galah-x/dashdisplay/pics/07_rear_and_front_asy_initial.jpg

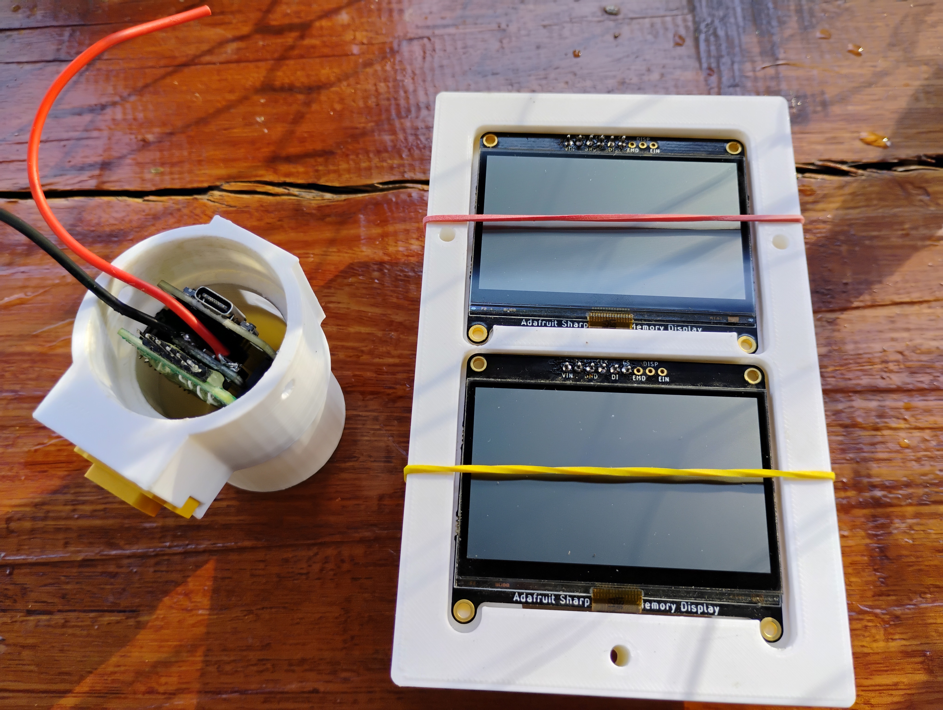
pics/07_rear_and_front_asy_initial.jpg
