galah-x/dashdisplay/pics/12_working_with_watchmon.jpg

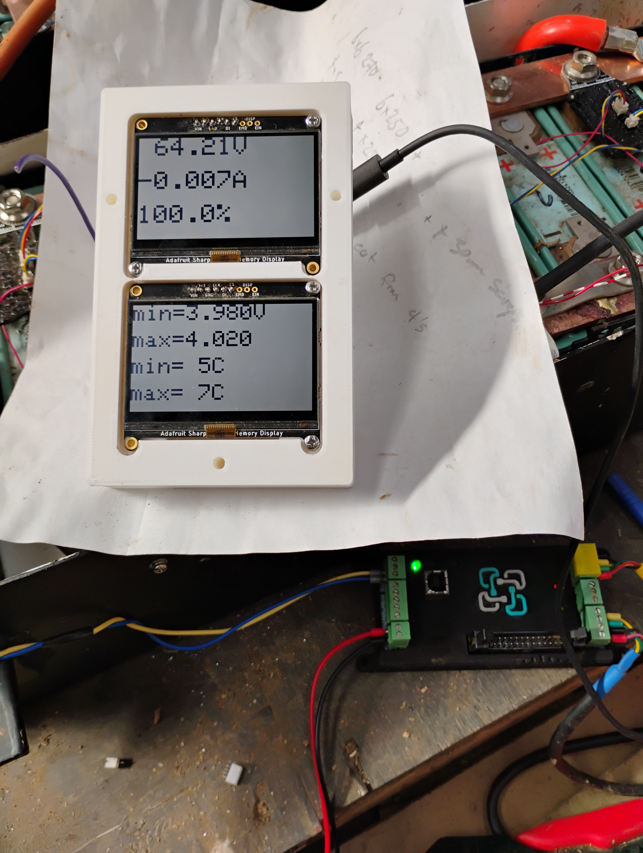
pics/12_working_with_watchmon.jpg
