galah-x/dashdisplay/pics/06_display_wiring_bd_fitted.jpg

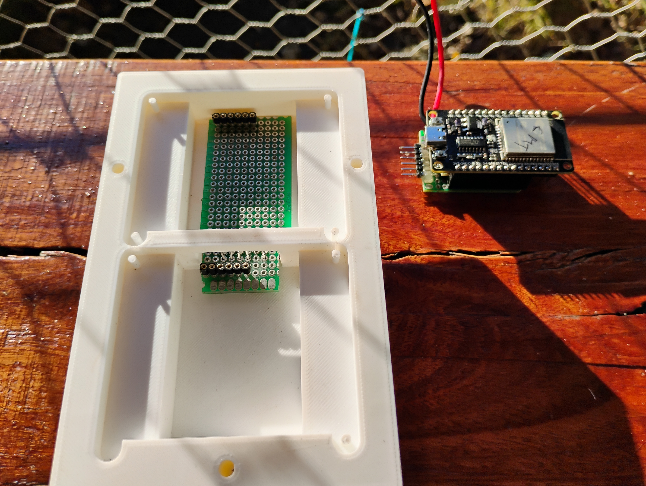
pics/06_display_wiring_bd_fitted.jpg
