galah-x/dashdisplay/schematics/dashdisplay_lcd_wiring/dashdisplay_lcd_wiring.kicad_sch

## KiCad design schematics/dashdisplay_lcd_wiring/dashdisplay_lcd_wiring.kicad_sch (2025-06-19)

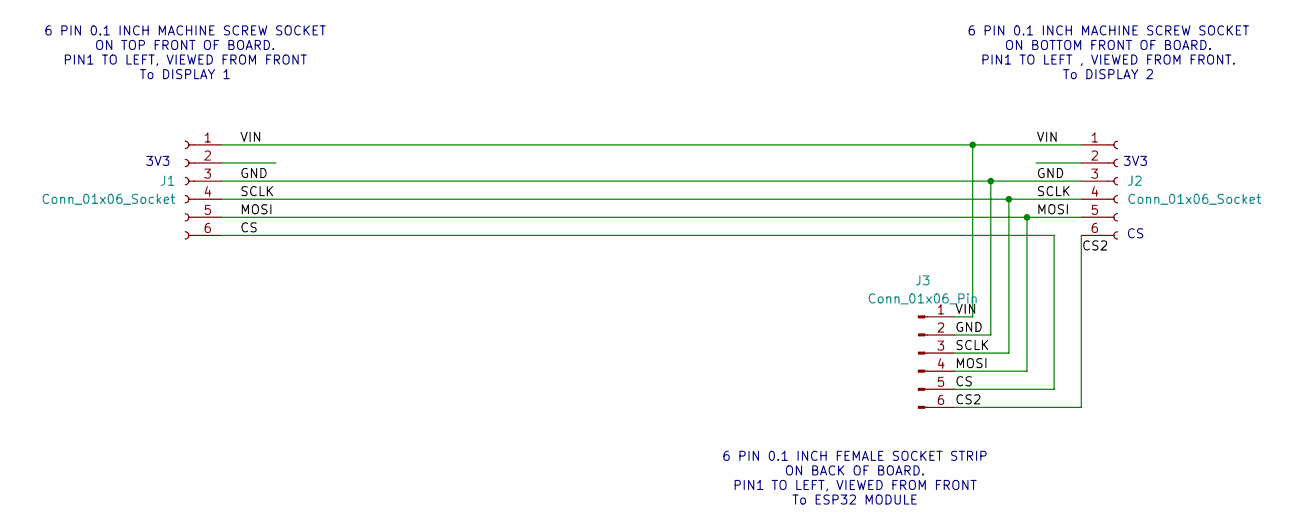
[picture p16: schematic dashdisplay_lcd_wiring.kicad_sch]

Parts:
J1, J2: Conn_01x06_Socket
J3: Conn_01x06_Pin

Connections:
CS: J1.6, J3.5
CS2: J2.6, J3.6
GND: J1.3, J2.3, J3.2
MOSI: J1.5, J2.5, J3.4
SCLK: J1.4, J2.4, J3.3
VIN: J1.1, J2.1, J3.1

Notes on the sheet:
6 PIN 0.1 INCH MACHINE SCREW SOCKET ON BOTTOM FRONT OF BOARD. PIN1 TO LEFT , VIEWED FROM FRONT. To DISPLAY 2
6 PIN 0.1 INCH FEMALE SOCKET STRIP ON BACK OF BOARD. PIN1 TO LEFT, VIEWED FROM FRONT To ESP32 MODULE
3V3
6 PIN 0.1 INCH MACHINE SCREW SOCKET ON TOP FRONT OF BOARD. PIN1 TO LEFT, VIEWED FROM FRONT To DISPLAY 1
