galah-x/dashdisplay/schematics/dashdisplay_motherboard/dashdisplay_motherboard.kicad_sch

## KiCad design schematics/dashdisplay_motherboard/dashdisplay_motherboard.kicad_sch (2025-06-19)

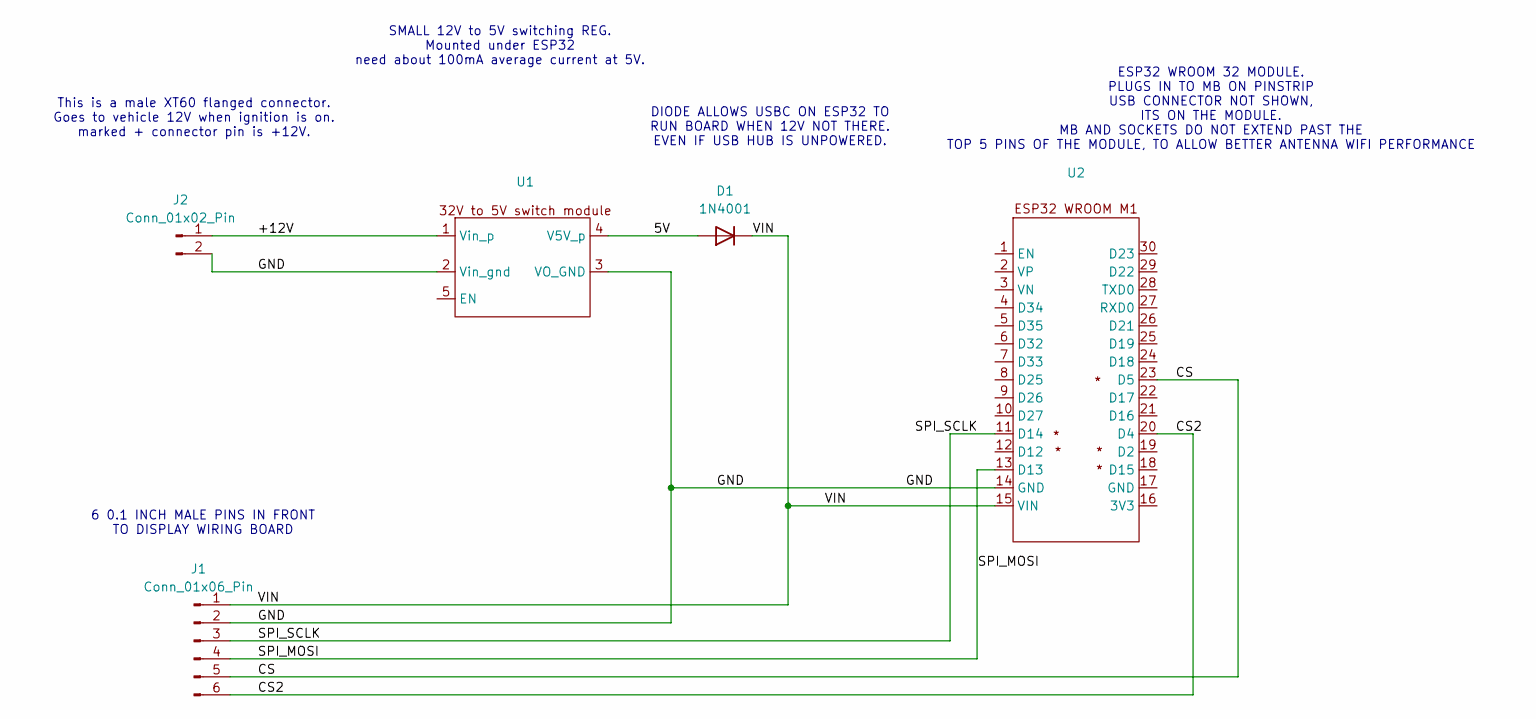
[picture p17: schematic dashdisplay_motherboard.kicad_sch]

Parts:
D1: 1N4001; D_DO-41_SOD81_P10.16mm_Horizontal
J1: Conn_01x06_Pin
J2: Conn_01x02_Pin
U1: switcher_en
U2: (no value)

Connections:
5V: D1.2 (A), U1.4 (V5V_p)
+12V: J2.1, U1.1 (Vin_p)
CS: J1.5, U2.23 (D5)
CS2: J1.6, U2.20 (D4)
GND: J1.2, J2.2, U1.2 (Vin_gnd), U1.3 (VO_GND), U2.14 (GND)
SPI_MOSI: J1.4, U2.13 (D13)
SPI_SCLK: J1.3, U2.11 (D14)
VIN: D1.1 (K), J1.1, U2.15 (VIN)

Notes on the sheet:
SMALL 12V to 5V switching REG. Mounted under ESP32 need about 100mA average current at 5V.
ESP32 WROOM 32 MODULE. PLUGS IN TO MB ON PINSTRIP USB CONNECTOR NOT SHOWN, ITS ON THE MODULE. MB AND SOCKETS DO NOT EXTEND PAST THE TOP 5 PINS OF THE MODULE, TO ALLOW BETTER ANTENNA WIFI PERFORMANCE
6 0.1 INCH MALE PINS IN FRONT TO DISPLAY WIRING BOARD
DIODE ALLOWS USBC ON ESP32 TO RUN BOARD WHEN 12V NOT THERE. EVEN IF USB HUB IS UNPOWERED.
This is a male XT60 flanged connector. Goes to vehicle 12V when ignition is on. marked + connector pin is +12V.
